hbekel/keyman64/protocol.h

#ifndef PROTOCOL_H
#define PROTOCOL_H

#define KEYMAN64_CTRL     0x00
#define KEYMAN64_STATE    0x01 // deprecated
#define KEYMAN64_IDENTIFY 0x02
#define KEYMAN64_FLASH    0x03
#define KEYMAN64_BOOT     0x04
#define KEYMAN64_KEY_DOWN 0x05
#define KEYMAN64_KEY_UP   0x06
#define KEYMAN64_RESET    0x07

#endif // PROTOCOL_H
