hbekel/keyman64/serial.h

/* -*- mode: kasm -*- */

.namespace Command {
.label none  = $00
.label exec  = $01
.label down  = $02
.label up    = $03
.label press = $04
.label map   = $05
.label set   = $06
.label type  = $07
}
