hbekel/keyman64/keyboard.h

#ifndef KEYBOARD_H
#define KEYBOARD_H

#define KEY_NONE      255

#define KEY_INSTDEL   0
#define KEY_3         1
#define KEY_5         2
#define KEY_7         3
#define KEY_9         4
#define KEY_PLUS      5
#define KEY_POUND     6
#define KEY_1         7

#define KEY_RETURN    8
#define KEY_W         9
#define KEY_R         10
#define KEY_Y         11
#define KEY_I         12
#define KEY_P         13
#define KEY_ASTERISK  14
#define KEY_BACKARROW 15

#define KEY_CURSORLEFT 16
#define KEY_A          17
#define KEY_D          18
#define KEY_G          19
#define KEY_J          20
#define KEY_L          21
#define KEY_SEMICOLON  22
#define KEY_CONTROL    23

#define KEY_F7         24
#define KEY_4          25
#define KEY_6          26
#define KEY_8          27
#define KEY_0          28
#define KEY_MINUS      29
#define KEY_CLRHOME    30
#define KEY_2          31

#define KEY_F1         32
#define KEY_Z          33
#define KEY_C          34
#define KEY_B          35
#define KEY_M          36
#define KEY_PERIOD     37
#define KEY_SHIFTRIGHT 38
#define KEY_SPACE      39

#define KEY_F3         40
#define KEY_S          41
#define KEY_F          42
#define KEY_H          43
#define KEY_K          44
#define KEY_COLON      45
#define KEY_EQUAL      46
#define KEY_CBM        47

#define KEY_F5         48
#define KEY_E          49
#define KEY_T          50
#define KEY_U          51
#define KEY_O          52
#define KEY_AT         53
#define KEY_UPARROW    54
#define KEY_Q          55

#define KEY_DOWNCURSOR 56
#define KEY_SHIFTLEFT  57
#define KEY_X          58
#define KEY_V          59
#define KEY_N          60
#define KEY_COMMA      61
#define KEY_SLASH      62
#define KEY_RUNSTOP    63

// SPECIAL SLOTS

#define KEY_LOCKED        0xfa
#define KEY_UNLOCKED      0xf9

#endif // KEYBOARD_H
